x893/TinyG/xboot/xboot-BT/xboot/api.h

#ifndef __API_H
#define __API_H

#include "xboot.h"
#include <avr/pgmspace.h>

// defines
// offsets and addresses
#ifndef PROGMEM_SIZE
	#define PROGMEM_SIZE (FLASHEND + 1UL)
#endif

#ifndef BOOT_SECTION_SIZE
	#error BOOT_SECTION_SIZE not defined!
#endif

#ifndef BOOT_SECTION_START
	#define BOOT_SECTION_START	(PROGMEM_SIZE - BOOT_SECTION_SIZE)
#endif

#ifndef APP_SECTION_START
	#define APP_SECTION_START	0
#endif

#ifndef APP_SECTION_SIZE
	#define APP_SECTION_SIZE	(PROGMEM_SIZE - BOOT_SECTION_SIZE)
#endif

#ifndef APP_SECTION_END
	#define APP_SECTION_END		(APP_SECTION_START + APP_SECTION_SIZE - 1UL)
#endif

#define JUMP_TABLE_LOCATION	(BOOT_SECTION_START + _VECTORS_SIZE)
#define JUMP_TABLE_INDEX(k)	(JUMP_TABLE_LOCATION + 4 + 2 * (k))

#define XB_APP_START		APP_SECTION_START
#define XB_APP_SIZE			(APP_SECTION_SIZE / 2)
#define XB_APP_END			(XB_APP_START + XB_APP_SIZE - 1UL)
#define XB_APP_TEMP_START	(XB_APP_END + 1UL)
#define XB_APP_TEMP_SIZE	XB_APP_SIZE
#define XB_APP_TEMP_END		(XB_APP_TEMP_START + XB_APP_TEMP_SIZE - 1UL)

// status codes
#define XB_SUCCESS 0
#define XB_ERR_NO_API 1
#define XB_ERR_NOT_FOUND 2
#define XB_INVALID_ADDRESS 3

// jump table struct
struct xboot_jump_table_s {
        uint8_t id[3];
        uint8_t ver;
        uint16_t ptr[];
};

// Functions

// General Functions
uint8_t xboot_get_version(uint16_t *ver);

// Low level flash access
uint8_t xboot_spm_wrapper(void);
uint8_t xboot_erase_application_page(uint32_t address);
uint8_t xboot_write_application_page(uint32_t address, uint8_t *data, uint8_t erase);
uint8_t xboot_write_user_signature_row(uint8_t *data);

// Higher level firmware update functions
uint8_t xboot_app_temp_erase(void);
uint8_t xboot_app_temp_write_page(uint32_t addr, uint8_t *data, uint8_t erase);

#endif // __API_H
