x893/TinyG/xboot/xboot-BT/xboot/flash.h

#ifndef __FLASH_H
#define __FLASH_H

#include <avr/io.h>
#include <avr/interrupt.h>

#include "sp_driver.h"
#include "xboot.h"

// offsets and addresses
#ifndef PROGMEM_SIZE
	#define PROGMEM_SIZE (FLASHEND + 1UL)
#endif

#ifndef BOOT_SECTION_SIZE
	#error BOOT_SECTION_SIZE not defined!
#endif

#ifndef BOOT_SECTION_START
	#define BOOT_SECTION_START (PROGMEM_SIZE - BOOT_SECTION_SIZE)
#endif

#ifndef APP_SECTION_START
	#define APP_SECTION_START 0
#endif

#ifndef APP_SECTION_SIZE
	#define APP_SECTION_SIZE (PROGMEM_SIZE - BOOT_SECTION_SIZE)
#endif

#ifndef APP_SECTION_END
	#define APP_SECTION_END (APP_SECTION_START + APP_SECTION_SIZE - 1UL)
#endif

#if PROGMEM_SIZE > 0x010000
	#define PGM_READ_BYTE	pgm_read_byte_far
	#define PGM_READ_WORD	pgm_read_word_far
	#define PGM_READ_DWORD	pgm_read_dword_far
#else
	#define PGM_READ_BYTE	pgm_read_byte_near
	#define PGM_READ_WORD	pgm_read_word_near
	#define PGM_READ_DWORD	pgm_read_dword_near
#endif

#define Flash_ReadByte SP_ReadByte
#define Flash_ReadWord SP_ReadWord
#define Flash_LoadFlashWord SP_LoadFlashWord
#define Flash_EraseApplicationSection SP_EraseApplicationSection
#define Flash_EraseApplicationPage SP_EraseApplicationPage
#define Flash_EraseWriteApplicationPage SP_EraseWriteApplicationPage
#define Flash_WriteApplicationPage SP_WriteApplicationPage
#define Flash_EraseUserSignatureRow SP_EraseUserSignatureRow
#define Flash_WriteUserSignatureRow SP_WriteUserSignatureRow
#define Flash_LoadFlashPage SP_LoadFlashPage
#define Flash_ReadFlashPage SP_ReadFlashPage
#define Flash_WaitForSPM SP_WaitForSPM

void Flash_ProgramPage(uint32_t page, uint8_t *buf, uint8_t erase);

#endif // __FLASH_H
